David-Feldt/xblinds/examples/Blinds Smart Home Automation - 4966303/images/IMG_7943.jpeg

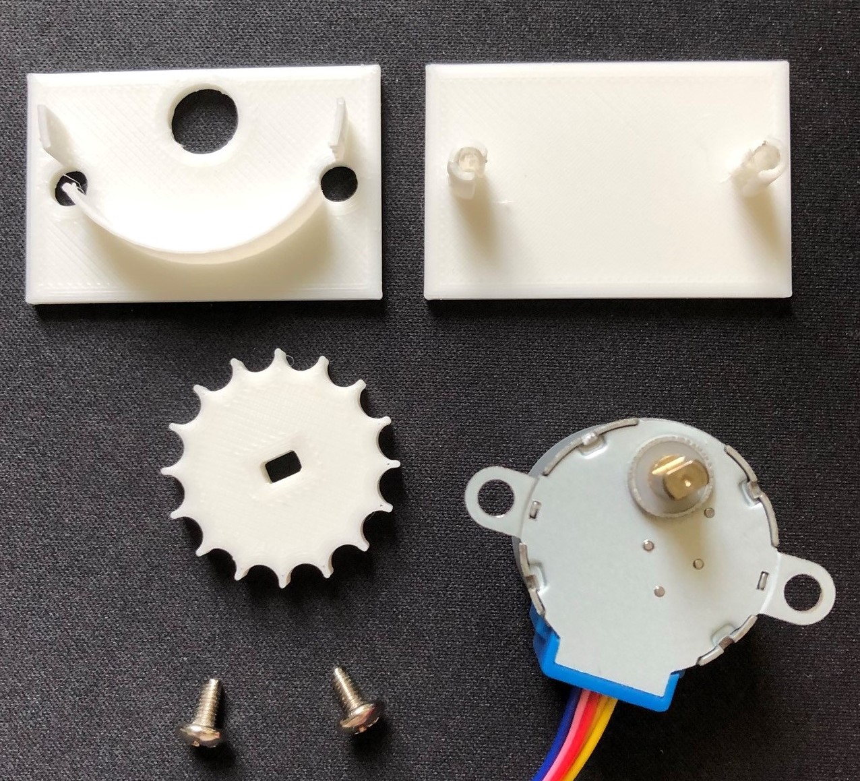
examples/Blinds Smart Home Automation - 4966303/images/IMG_7943.jpeg
