David-Feldt/xblinds/examples/Blinds Smart Home Automation - 4966303/images/IMG_7944.jpeg

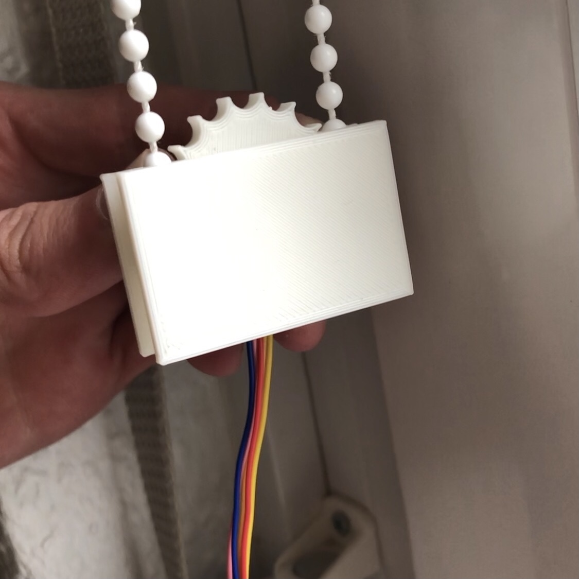
examples/Blinds Smart Home Automation - 4966303/images/IMG_7944.jpeg
