David-Feldt/xblinds/examples/Blinds Smart Home Automation - 4966303/images/Smart_Home_-_Gear_Holder_1-2.png

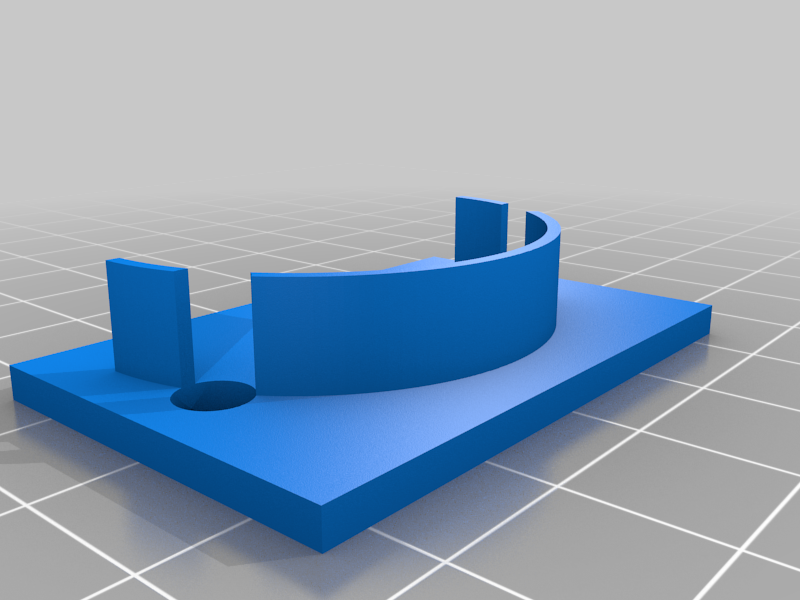
examples/Blinds Smart Home Automation - 4966303/images/Smart_Home_-_Gear_Holder_1-2.png
