David-Feldt/xblinds/examples/Minimalistic Motorized Roller Blinds - NEMA 17 stepper motor gear and mount - 5965826/images/884b0b1f-9aca-4883-86ce-a96ea89ef9b4.png

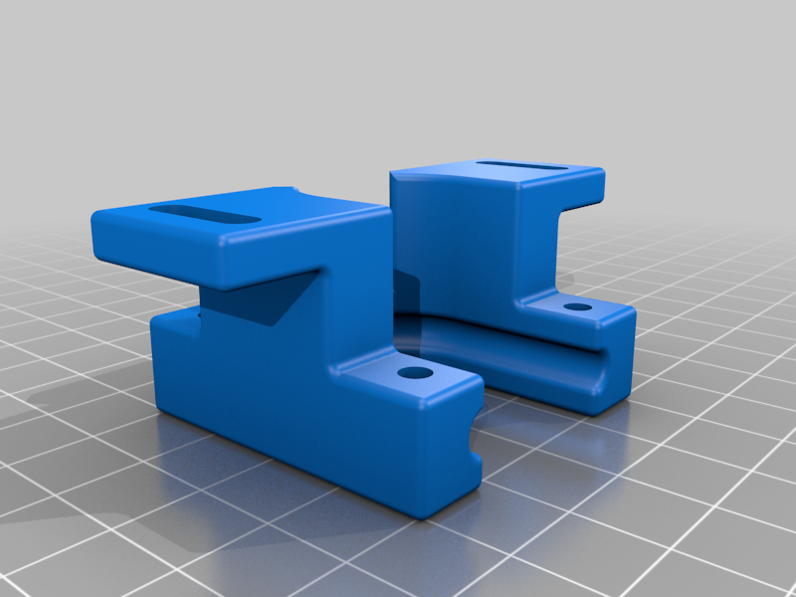
examples/Minimalistic Motorized Roller Blinds - NEMA 17 stepper motor gear and mount - 5965826/images/884b0b1f-9aca-4883-86ce-a96ea89ef9b4.png
