David-Feldt/xblinds/examples/Minimalistic Motorized Roller Blinds - NEMA 17 stepper motor gear and mount - 5965826/images/bf1fdc2e-7e7b-40a5-b321-069fb7cf7333.JPEG

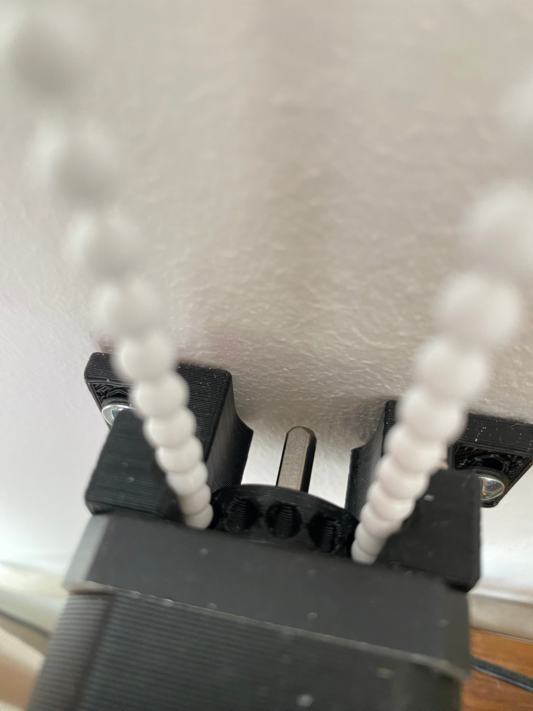
examples/Minimalistic Motorized Roller Blinds - NEMA 17 stepper motor gear and mount - 5965826/images/bf1fdc2e-7e7b-40a5-b321-069fb7cf7333.JPEG
