David-Feldt/xblinds/examples/xBlinds - 4792584/images/BoxBottom.png

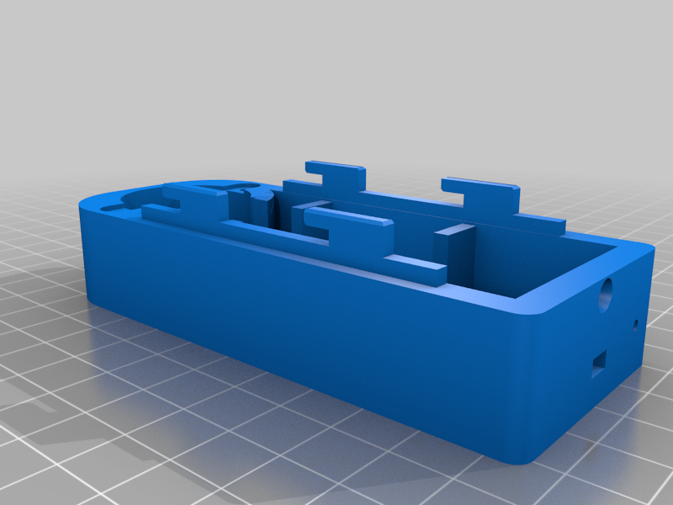
examples/xBlinds - 4792584/images/BoxBottom.png
