David-Feldt/xblinds/examples/xBlinds - 4792584/images/BoxTop-ButtonHole.png

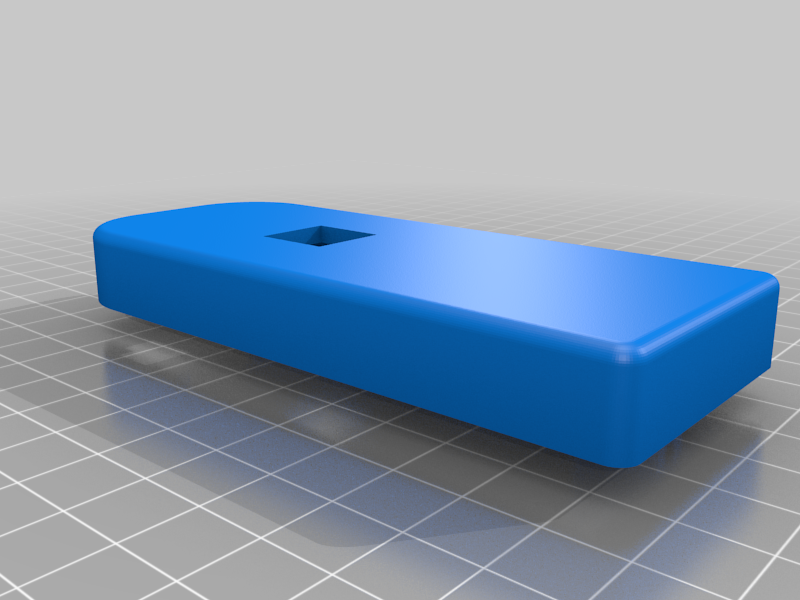
examples/xBlinds - 4792584/images/BoxTop-ButtonHole.png
