David-Feldt/xblinds/examples/xBlinds - 4792584/images/button-base.jpg

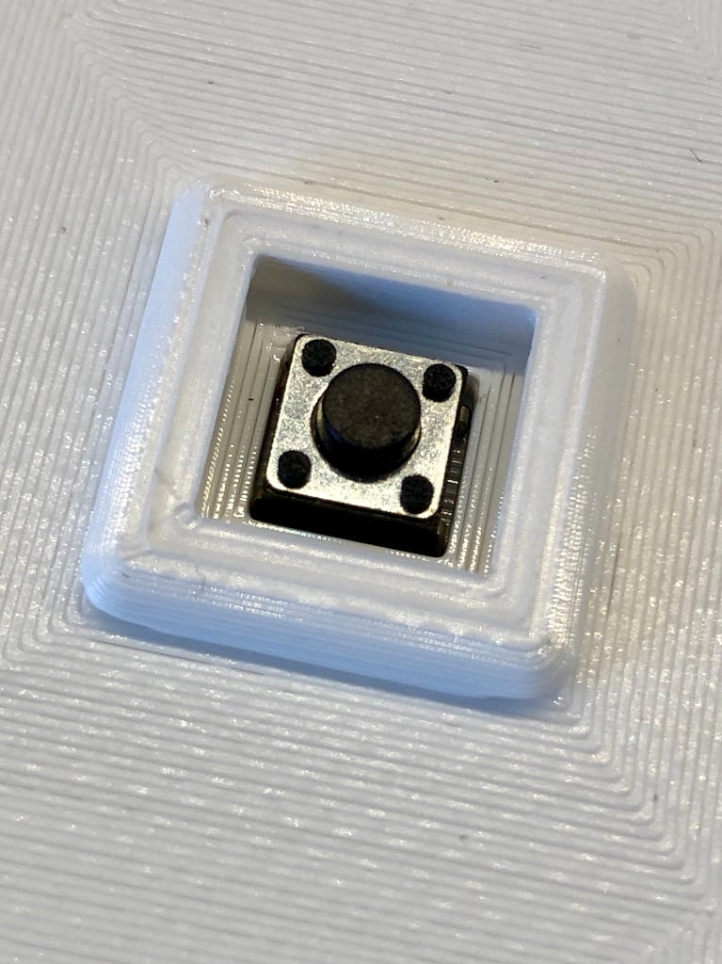
examples/xBlinds - 4792584/images/button-base.jpg
