David-Feldt/xblinds/examples/xBlinds - 4792584/images/button-top.jpg

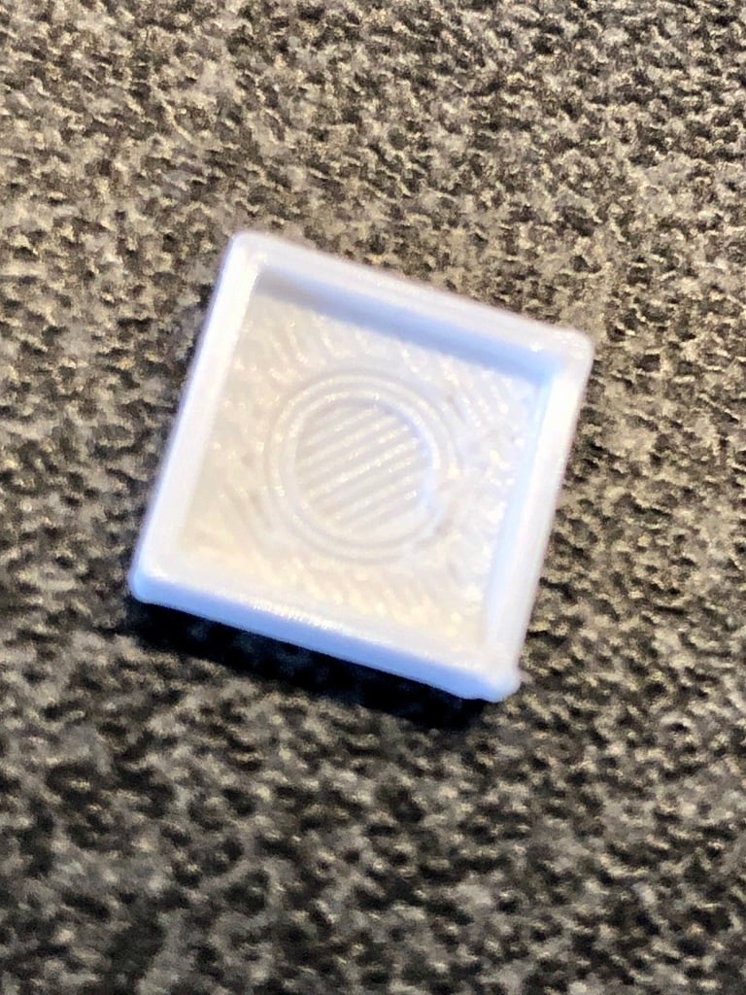
examples/xBlinds - 4792584/images/button-top.jpg
