David-Feldt/xblinds/examples/xBlinds - 4792584/images/button.jpg

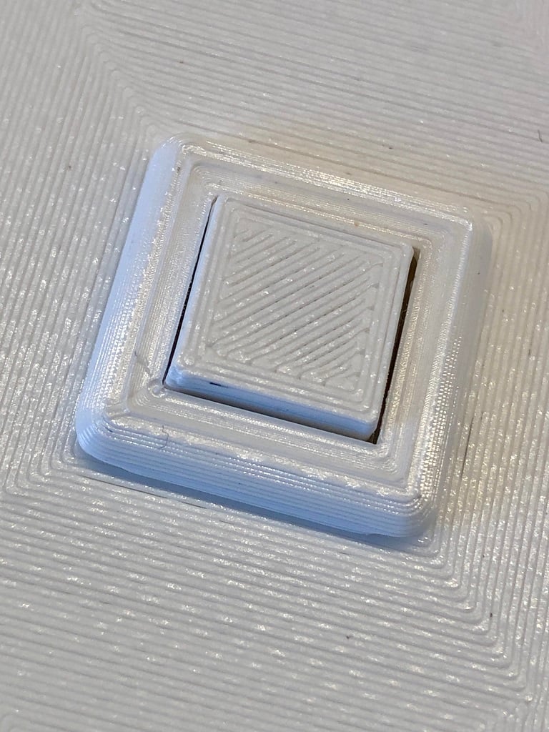
examples/xBlinds - 4792584/images/button.jpg
