David-Feldt/xblinds/examples/xBlinds - 4792584/images/Pulley-40deg.png

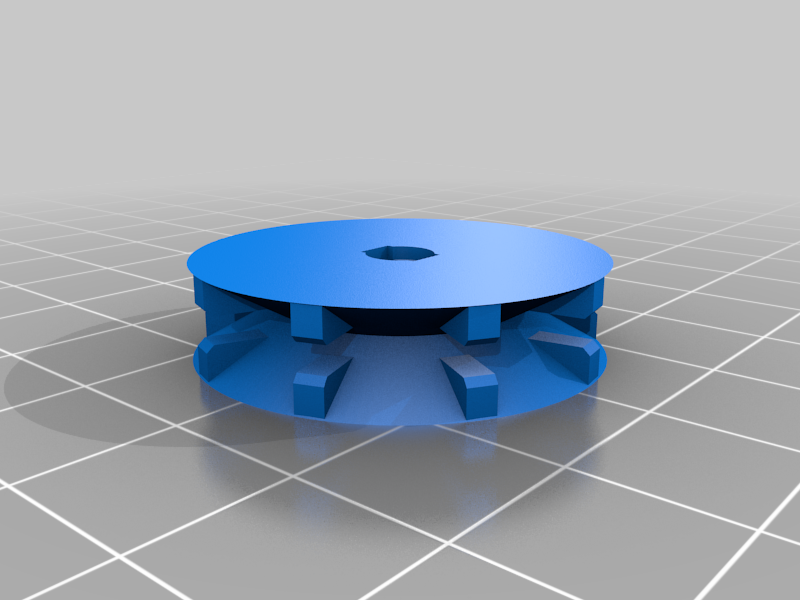
examples/xBlinds - 4792584/images/Pulley-40deg.png
