David-Feldt/xblinds/examples/xBlinds - 4792584/images/Tactile_Button_Base_Rounded.png

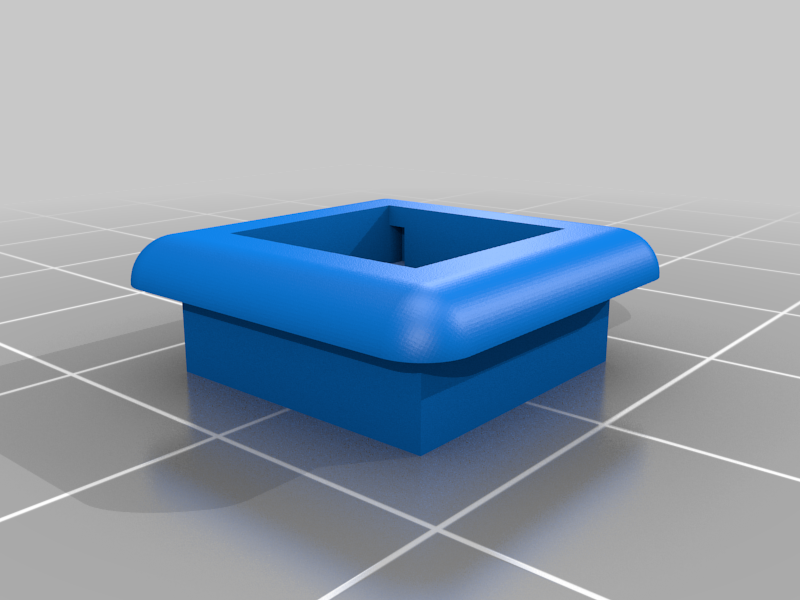
examples/xBlinds - 4792584/images/Tactile_Button_Base_Rounded.png
