David-Feldt/xblinds/examples/xBlinds - 4792584/images/Tactile_Button_Base_Square.png

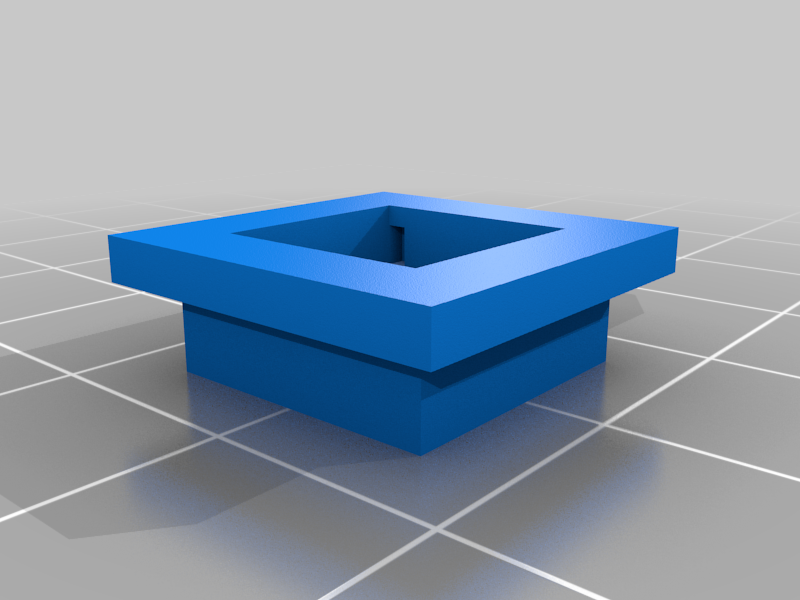
examples/xBlinds - 4792584/images/Tactile_Button_Base_Square.png
