David-Feldt/xblinds/examples/xBlinds - 4792584/images/xblinds-mounted.jpg

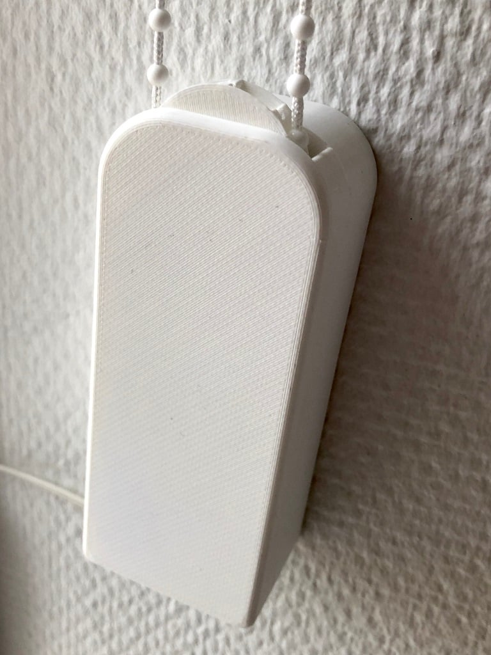
examples/xBlinds - 4792584/images/xblinds-mounted.jpg
