David-Feldt/xblinds/examples/xBlinds - 4792584/images/xblinds-open.jpg

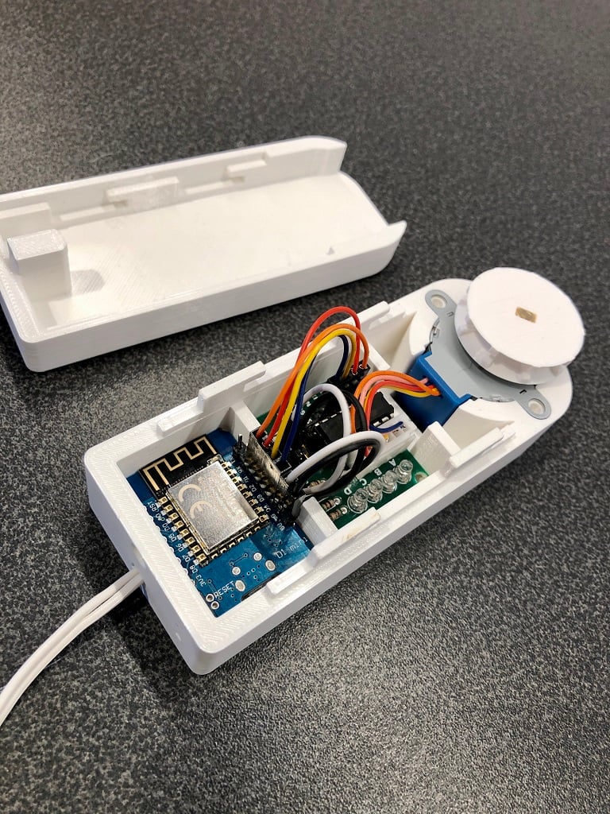
examples/xBlinds - 4792584/images/xblinds-open.jpg
