David-Feldt/xblinds/mechanical/xblinds v5.3mf

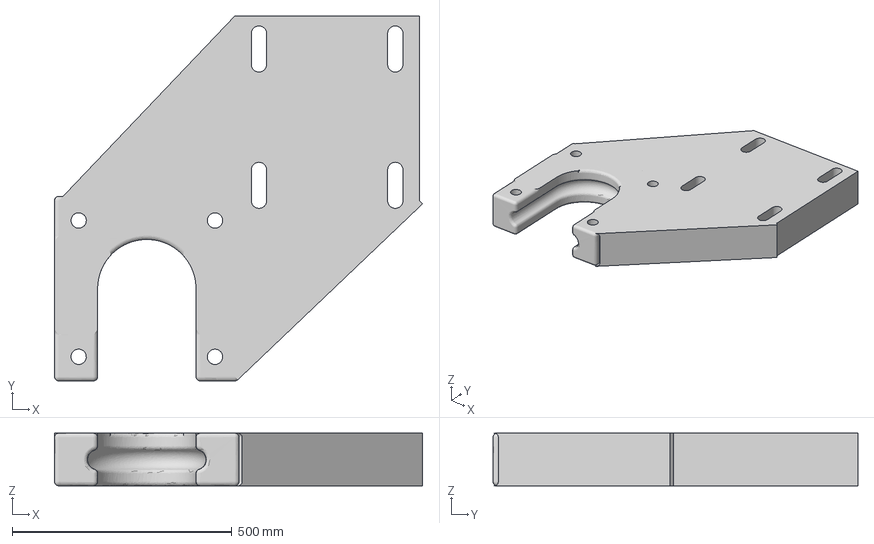
[picture p36: CAD file, 2025-04-22]
mechanical/xblinds v5.3mf
836.9 x 830.0 x 120.0 mm
