David-Feldt/xblinds/mechanical/blinds_holder.stl

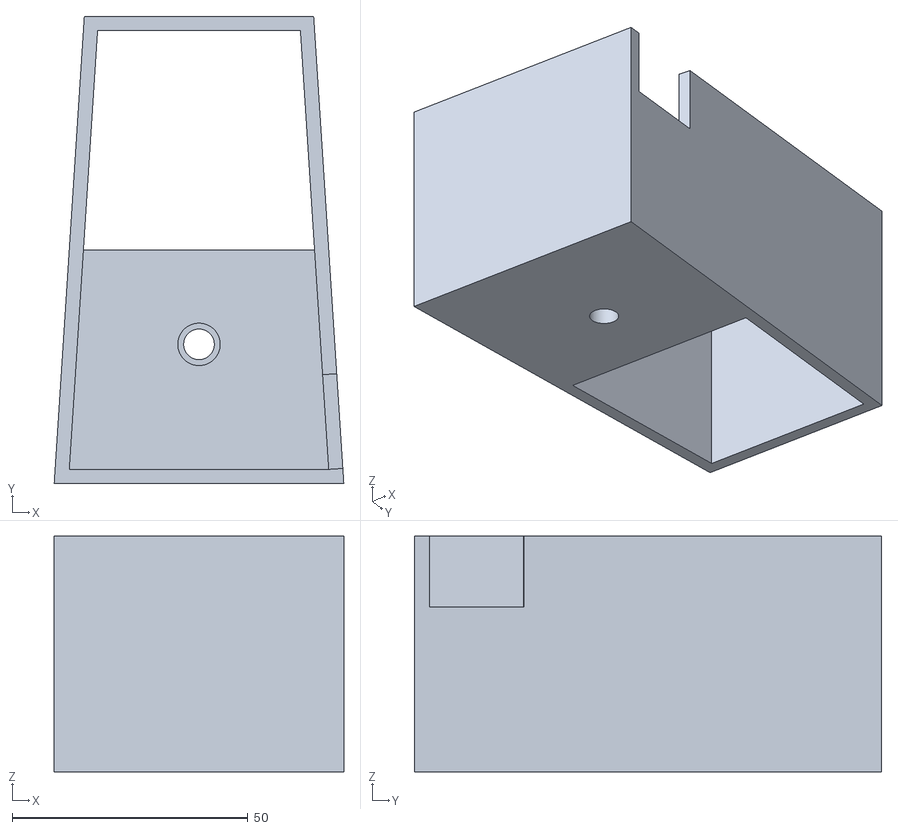
[picture p37: CAD file, 2025-04-22]
mechanical/blinds_holder.stl
61.4 x 99.0 x 50.0
