David-Feldt/xblinds/mechanical/Gear 1.stl

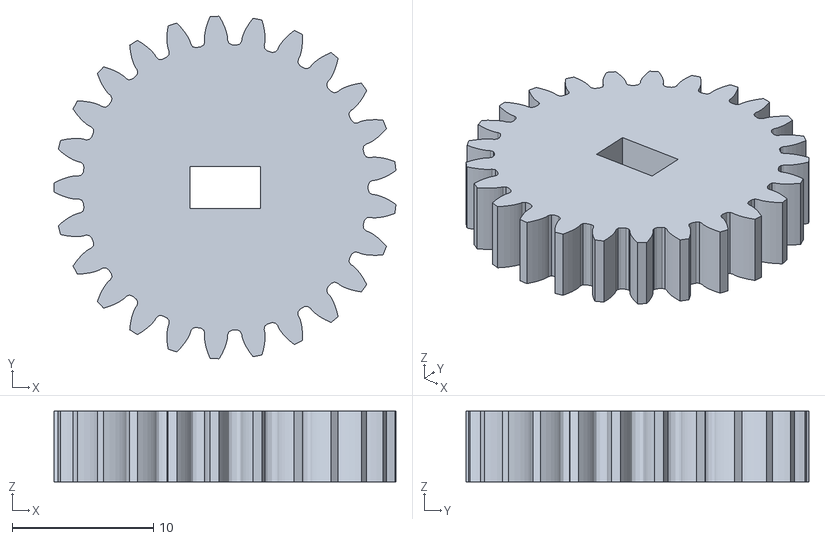
[picture p38: CAD file, 2025-04-22]
mechanical/Gear 1.stl
24.2 x 24.3 x 5.00
