David-Feldt/xblinds/software/sketch_mar31a_copy_20250411184948/sketch_mar31a_copy_20250411184948.ino

// Include the Arduino Stepper Library
#include <Stepper.h>

// Number of steps per output rotation
const int stepsPerRevolution = 200;

// Create Instance of Stepper library
// Stepper myStepper(stepsPerRevolution, 8, 9, 10, 11);
Stepper myStepper(stepsPerRevolution, D1, D2, D3, D4);




void setup()
{
	// set the speed at 60 rpm:
	myStepper.setSpeed(60);
	// initialize the serial port:
	Serial.begin(9600);
}

void loop() 
{
	// step one revolution in one direction:
	Serial.println("clockwise");
	myStepper.step(stepsPerRevolution);
	delay(500);

	// step one revolution in the other direction:
	Serial.println("counterclockwise");
	myStepper.step(-stepsPerRevolution);
	delay(500);
}
